BernardoCastelo/Nixie_tube_clock/00.Simulations/dc_dc boost.asc

C1: cap; 3µ; V=200 Irms=5.06 Rser=0.0268854 Lser=0
C2: cap; 100n
C3: cap; 1n
D1: diode; RF1501NS3S
D2: schottky; BAT54
D3: schottky; BAT54
L1: ind; 10µ
M1: nmos; BSC900N20NS3
Q1: npn; BC547C
R1: res; 220k
R2: res; 680
R3: res; 10k
R4: res; 1k
R_LOAD: res; 2k
rp1: res; 1k
rp2: res; 10k
U1: NE555
V1: voltage; 12
Named nets: vcc, v_out, 0, v_pwm, rst
.tran 0 10m 0 10n startup
