BernardoCastelo/Nixie_tube_clock/00.Simulations/dc_dc boostArduino.asc

C1: cap; 3µ; V=200 Irms=5.06 Rser=0.0268854 Lser=0
D1: diode; RF1501NS3S
L1: ind; 22µ
M1: nmos; BSC900N20NS3
R1: res; 220k
R2: res; 5.6k
R3: res; 100k
R4: res; 1k
R_LOAD: res; 2k
V1: voltage; 12
V2: voltage; PULSE(0 5 0 100n 100n 8u 16u)
Named nets: vcc, v_out, 0, v_pwm
.tran 0 10m 0 1u startup
